Aifryz/parkside-battery-hack/sch/charger/charger.kicad_sch

## KiCad design sch/charger/charger.kicad_sch (2023-03-18, an earlier design)

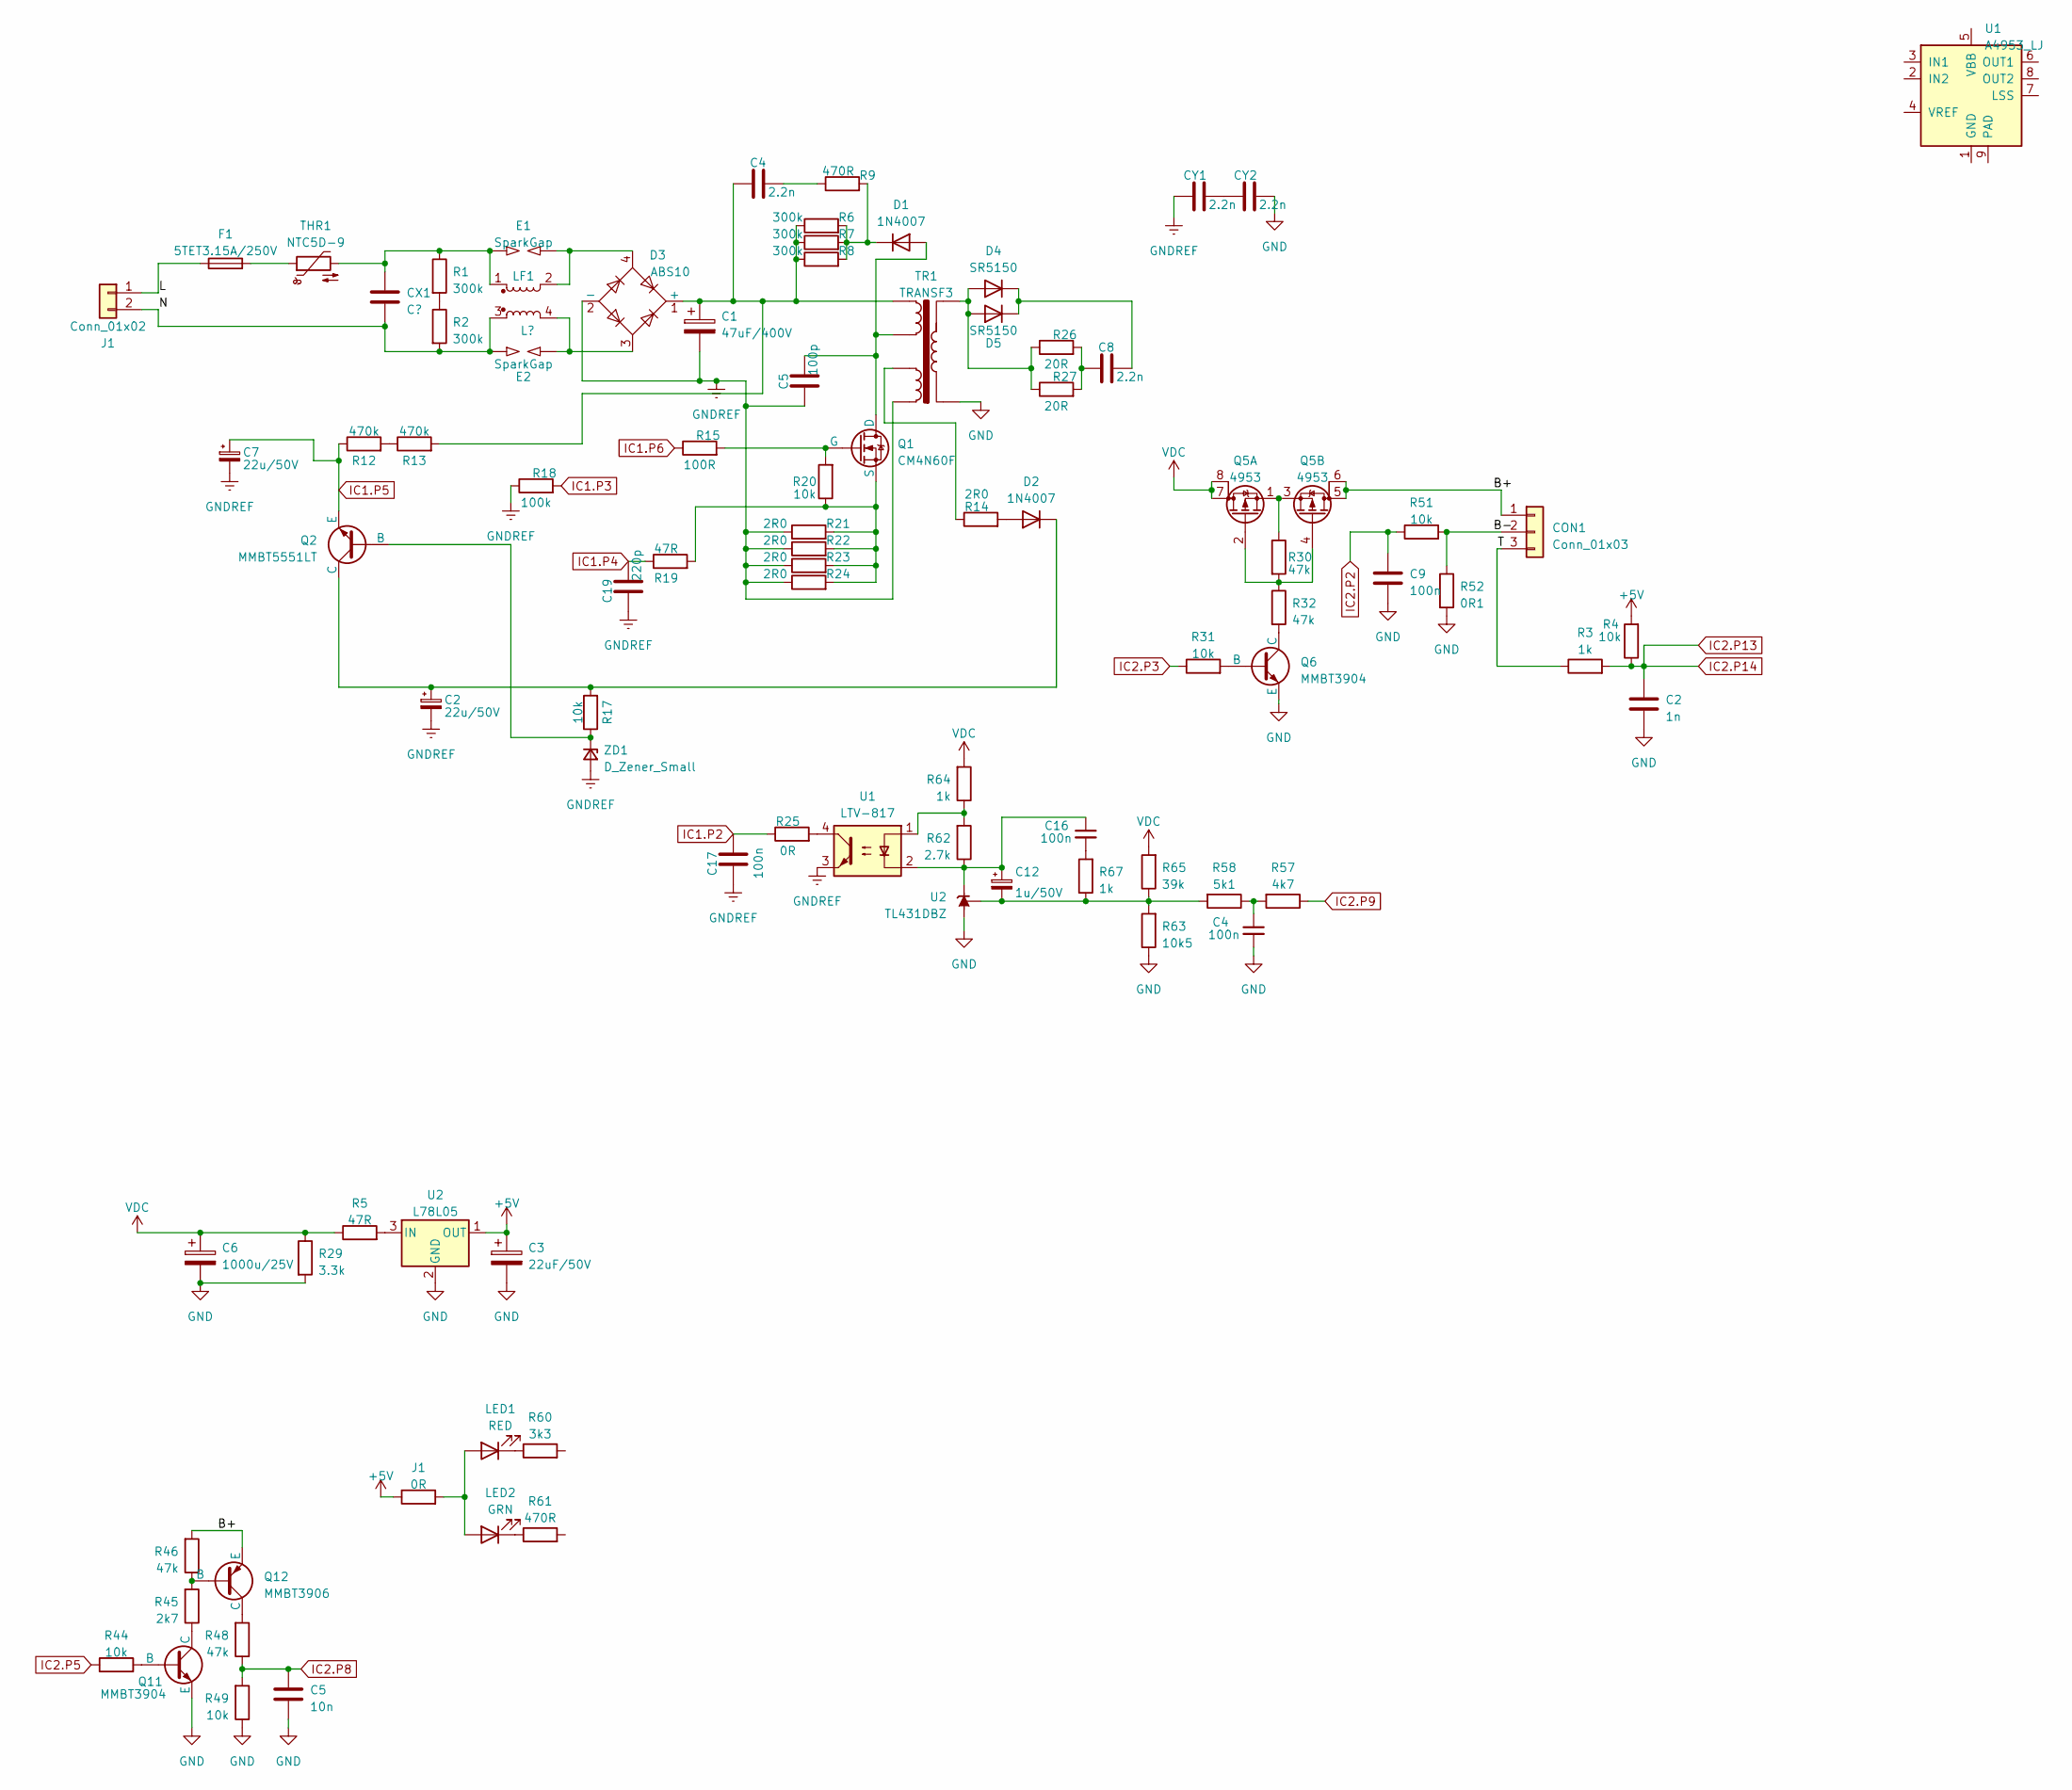
[picture p8: schematic charger.kicad_sch]

Parts:
C1: 47uF/400V
C2, C7: 22u/50V
C3: 22uF/50V
C4, C9, C16, C17: 100n
C5: 10n
C6: 1000u/25V
C8: 2.2n
C12: 1u/50V
C19: 220p
CON1: Conn_01x03
CX1: C?
CY1, CY2: 2.2n
D1, D2: 1N4007; D_DO-41_SOD81_P10.16mm_Horizontal
D3: ABS10; Diode_Bridge_Diotec_ABS
D4, D5: SR5150; D_DO-41_SOD81_P10.16mm_Horizontal
E1, E2: SparkGap
F1: 5TET3.15A/250V
J1: 0R
LED1: RED
LED2: GRN
LF1: L?
Q1: CM4N60F
Q2: MMBT5551LT
Q5: 4953
Q6, Q11: MMBT3904
Q12: MMBT3906
R1, R2, R6, R7, R8: 300k
R3, R64, R67: 1k
R4, R17, R20, R31, R44, R49, R51: 10k
R5, R19: 47R
R9, R61: 470R
R12, R13: 470k
R14, R21, R22, R23, R24: 2R0
R15: 100R
R18: 100k
R25: 0R
R26, R27: 20R
R29: 3.3k
R30, R32, R46, R48: 47k
R45: 2k7
R52: 0R1
R57: 4k7
R58: 5k1
R60: 3k3
R62: 2.7k
R63: 10k5
R65: 39k
THR1: NTC5D-9
TR1: TRANSF3
U1: LTV-817; DIP-4_W7.62mm
U2: TL431DBZ; SOT-23
ZD1: D_Zener_Small

Connections:
+5V: C3.1, J1.1, R4.2, U2.1 (OUT)
B+: CON1.1, Q5.5 (D), Q5.6 (G), Q12.3 (E), R46.2
B-: CON1.2, R51.2, R52.1
GND: C2.2, C3.2, C4.2, C5.2, C6.2, C9.2, CY2.2, Q6.3 (E), Q11.3 (E), R29.2, R49.1, R52.2, R63.1, TR1.1, U2.2 (GND), U2.3 (IN)
GNDREF: C1.2, C2.2, C5.1, C7.2, C17.1, C19.1, CY1.1, D3.2 (-), R18.1, R21.1, R22.1, R23.1, R24.1, TR1.3, U1.3 (IN1), ZD1.2 (A)
IC1.P2: C17.2, R25.1
IC1.P3: R18.2
IC1.P4: C19.2, R19.1
IC1.P5: C7.1, Q2.3 (E), R12.1
IC1.P6: R15.1
IC2.P2: C9.1, R51.1
IC2.P3: R31.1
IC2.P5: R44.1
IC2.P8: C5.1, R48.1, R49.2
IC2.P9: R57.1
IC2.P13: C2.1, R3.2, R4.1
L: F1.1, J1.1
N: CX1.2, E2.1, J1.2, LF1.3, R2.2
unnamed: C1.1, C4.1, D3.1 (+), R6.1, R7.1, R8.1, R13.2, TR1.6
unnamed: C2.1, D2.1 (K), Q2.1 (C), R17.2
unnamed: C4.1, R57.2, R58.1
unnamed: C4.2, R9.1
unnamed: C5.2, D1.2 (A), Q1.1 (D), TR1.5
unnamed: C8.1, R26.2, R27.2
unnamed: C8.2, D4.1 (K), D5.1 (K)
unnamed: C12.1, C16.1, R62.1, U1.2 (IN2), U2.1 (OUT)
unnamed: C12.2, R58.2, R63.2, R65.1, R67.1, U2.2 (GND)
unnamed: C16.2, R67.2
unnamed: CX1.1, E1.1, LF1.1, R1.1, THR1.2
unnamed: CY1.2, CY2.1
unnamed: D1.1 (K), R6.2, R7.2, R8.2, R9.2
unnamed: D2.2 (A), R14.2
unnamed: D3.3, E2.2, LF1.4
unnamed: D3.4, E1.2, LF1.2
unnamed: D4.2 (A), D5.2 (A), R26.1, R27.1, TR1.2
unnamed: F1.2, THR1.1
unnamed: J1.2, LED1.2 (A), LED2.2 (A)
unnamed: LED1.1 (K), R60.1
unnamed: LED2.1 (K), R61.1
unnamed: Q1.2 (G), R15.2, R20.2
unnamed: Q1.3 (S), R19.2, R20.1, R21.2, R22.2, R23.2, R24.2
unnamed: Q2.2 (B), R17.1, ZD1.1 (K)
unnamed: Q5.1 (S), Q5.3 (S), R30.1
unnamed: Q5.2 (G), Q5.4 (G), R30.2, R32.1
unnamed: Q6.1 (C), R32.2
unnamed: Q6.2 (B), R31.2
unnamed: Q11.1 (C), R45.1
unnamed: Q11.2 (B), R44.2
unnamed: Q12.1 (C), R48.2
unnamed: Q12.2 (B), R45.2, R46.1
unnamed: R1.2, R2.1
unnamed: R5.2, U2.3 (IN)
unnamed: R12.2, R13.1
unnamed: R14.1, TR1.4
unnamed: R25.2, U1.4 (VREF)
unnamed: R62.2, R64.1, U1.1 (GND)
T: CON1.3, R3.1
VDC: C6.1, Q5.7 (D), Q5.8 (G), R5.1, R29.1, R64.2, R65.2
